TikitaTolley/smart-plant-moisture-monitor/main/certificates.h

#pragma once

// Google Trust Services GTS Root R4, valid until 22 June 2036.
// The Cloudflare Worker certificate currently chains to this root.
constexpr char gtsRootR4[] = R"CERT(
-----BEGIN CERTIFICATE-----
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
-----END CERTIFICATE-----
)CERT";
