TikitaTolley/smart-plant-moisture-monitor/main/secrets.example.h

#pragma once

constexpr char WIFI_SSID[] = "your-wifi-name";
constexpr char WIFI_PASSWORD[] = "your-wifi-password";
constexpr char API_URL[] =
  "https://your-worker.workers.dev/api/v1/readings/";
constexpr char DEVICE_KEY[] = "replace-with-a-random-secret";
